stefanbaur/grannophone/case/sheet_4_siedle_noamp.pdf

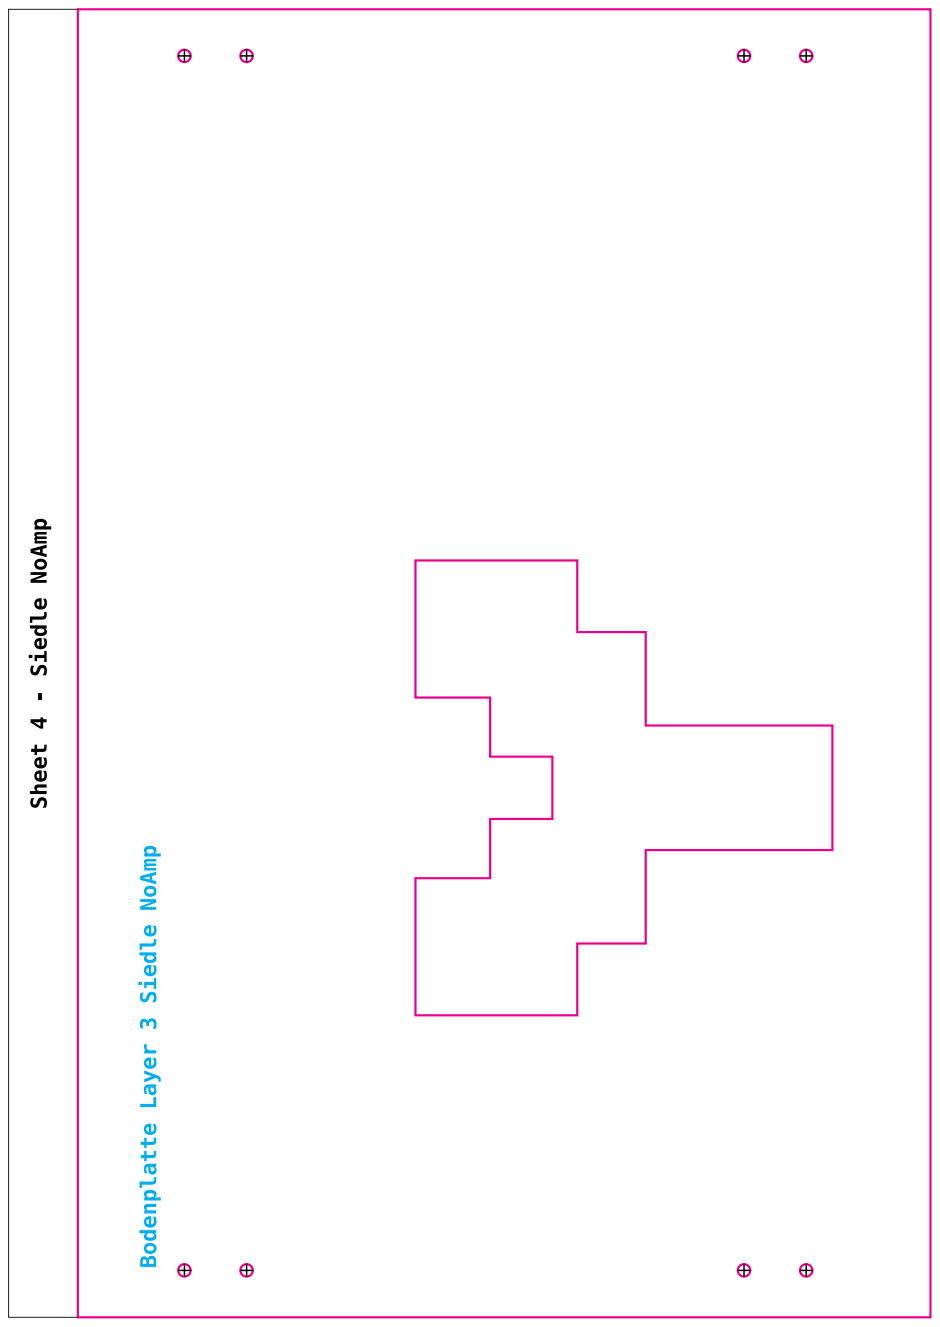
[picture p11: page 1]
