stefanbaur/grannophone/case/sheet_4_veco.pdf

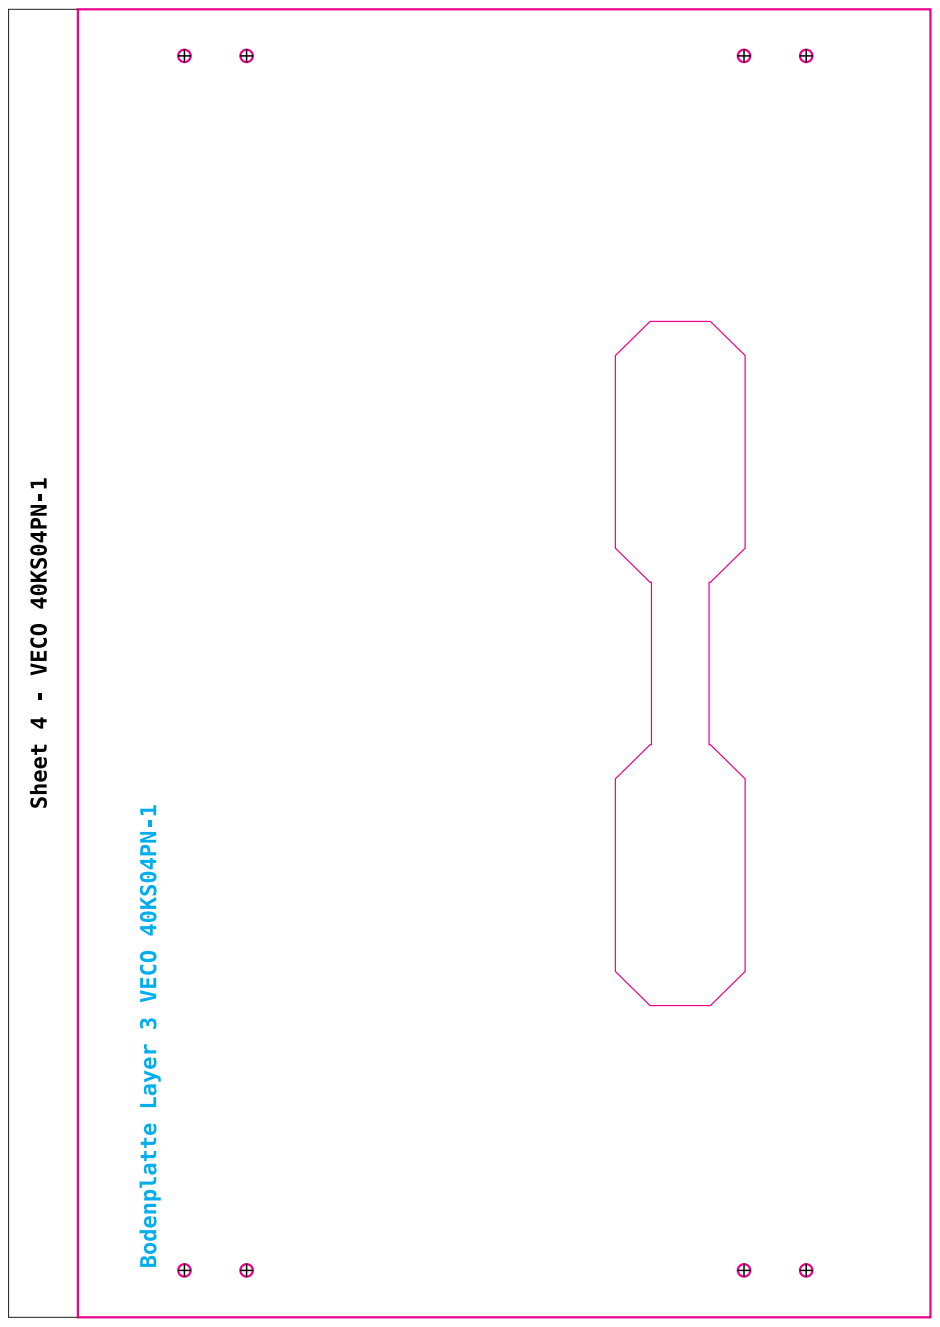
[picture p12: page 1]
