stefanbaur/grannophone/case/sheet_4_visaton_waveshare.pdf

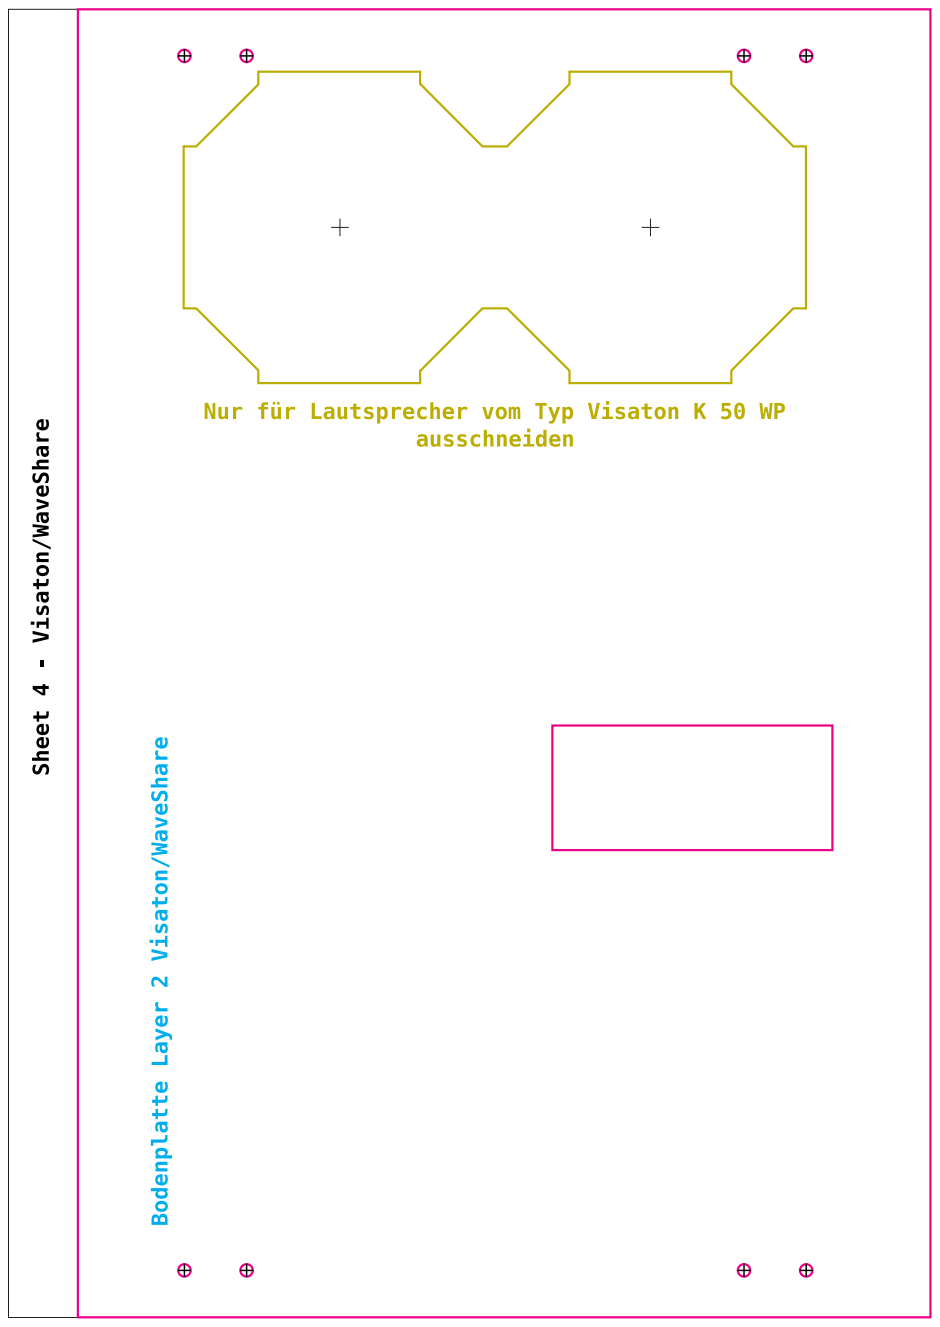
[picture p13: page 1]
