stefanbaur/grannophone/case/sheet_5_siedle_noamp.pdf

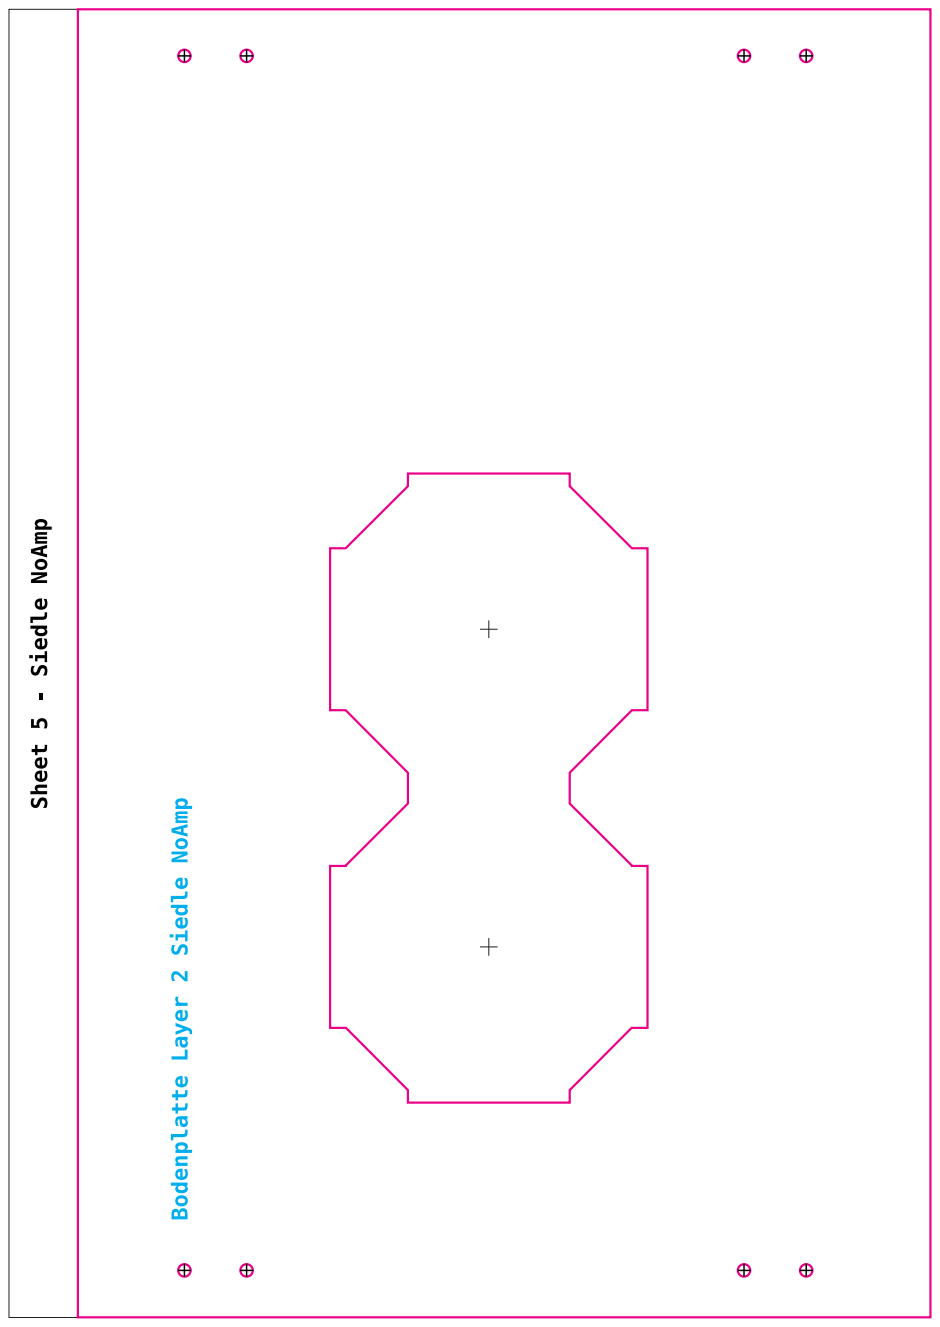
[picture p14: page 1]
