stefanbaur/grannophone/case/sheet_5_veco.pdf

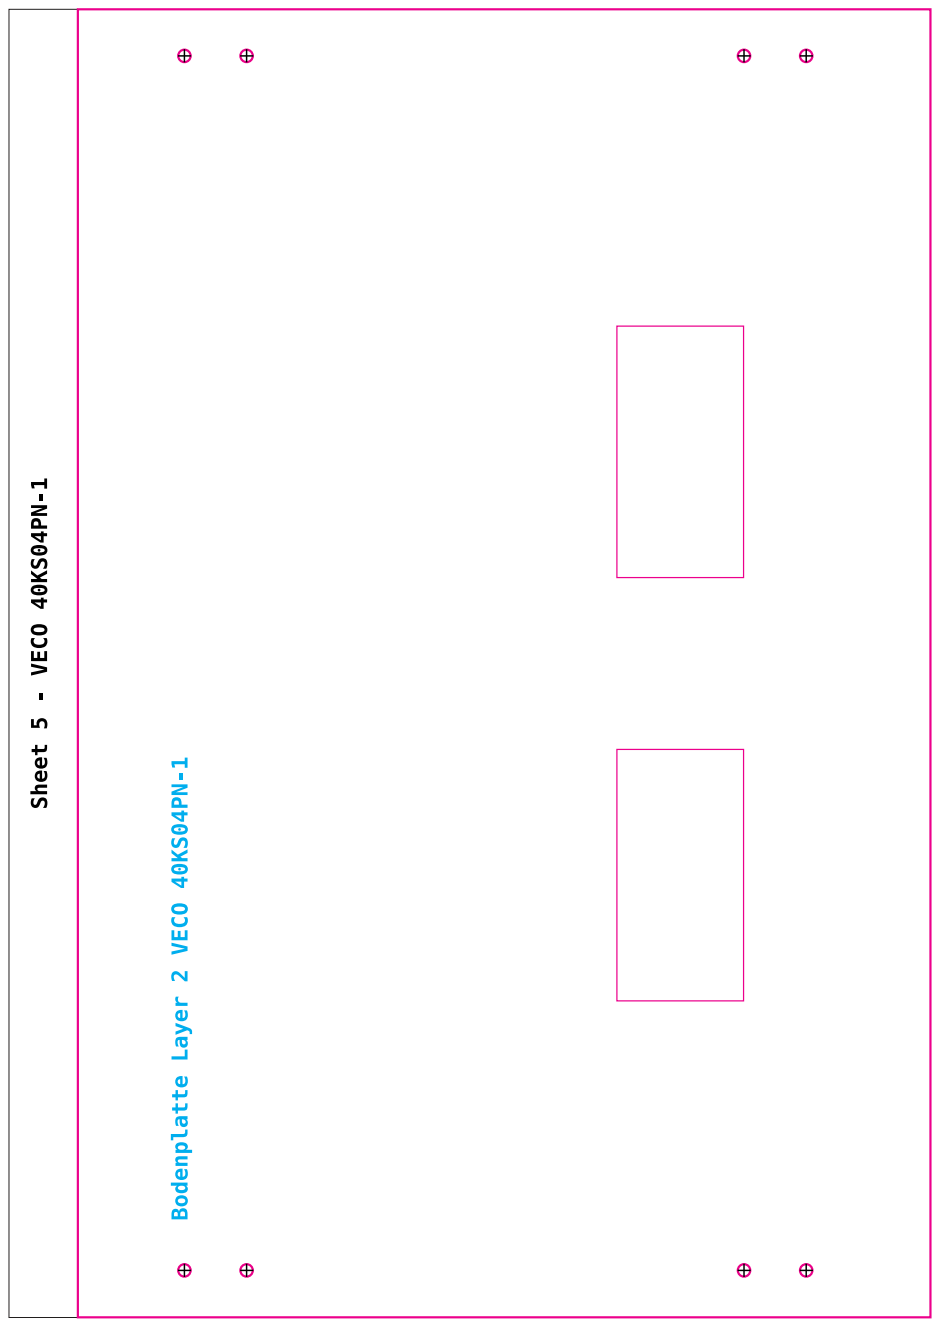
[picture p15: page 1]
