stefanbaur/grannophone/case/sheet_5_visaton.pdf

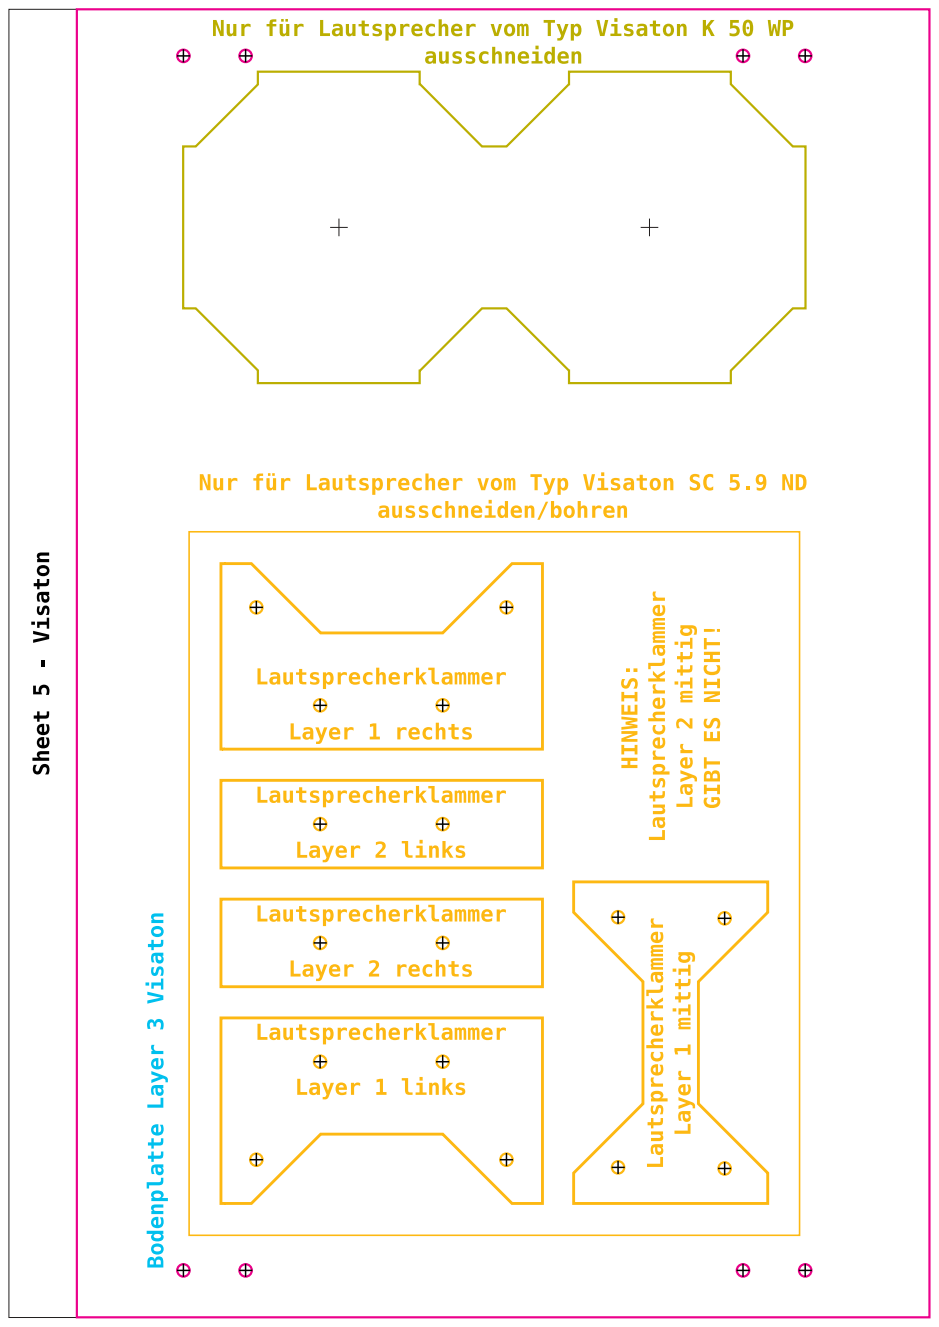
[picture p16: page 1]
