stefanbaur/grannophone/case/sheet_5_waveshare.pdf

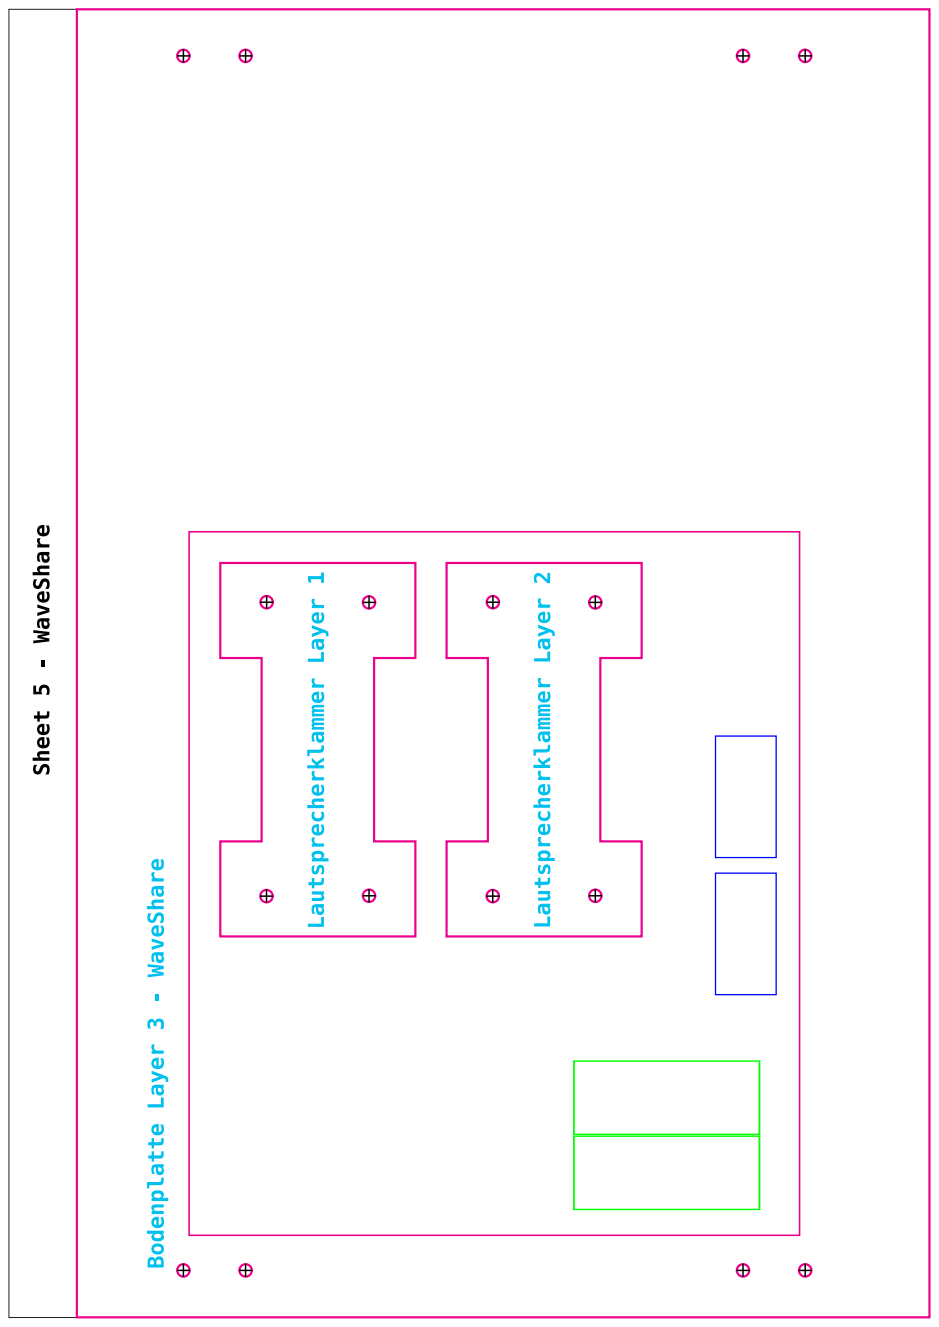
[picture p17: page 1]
