stefanbaur/grannophone/case/sheet_6_siedle_noamp.pdf

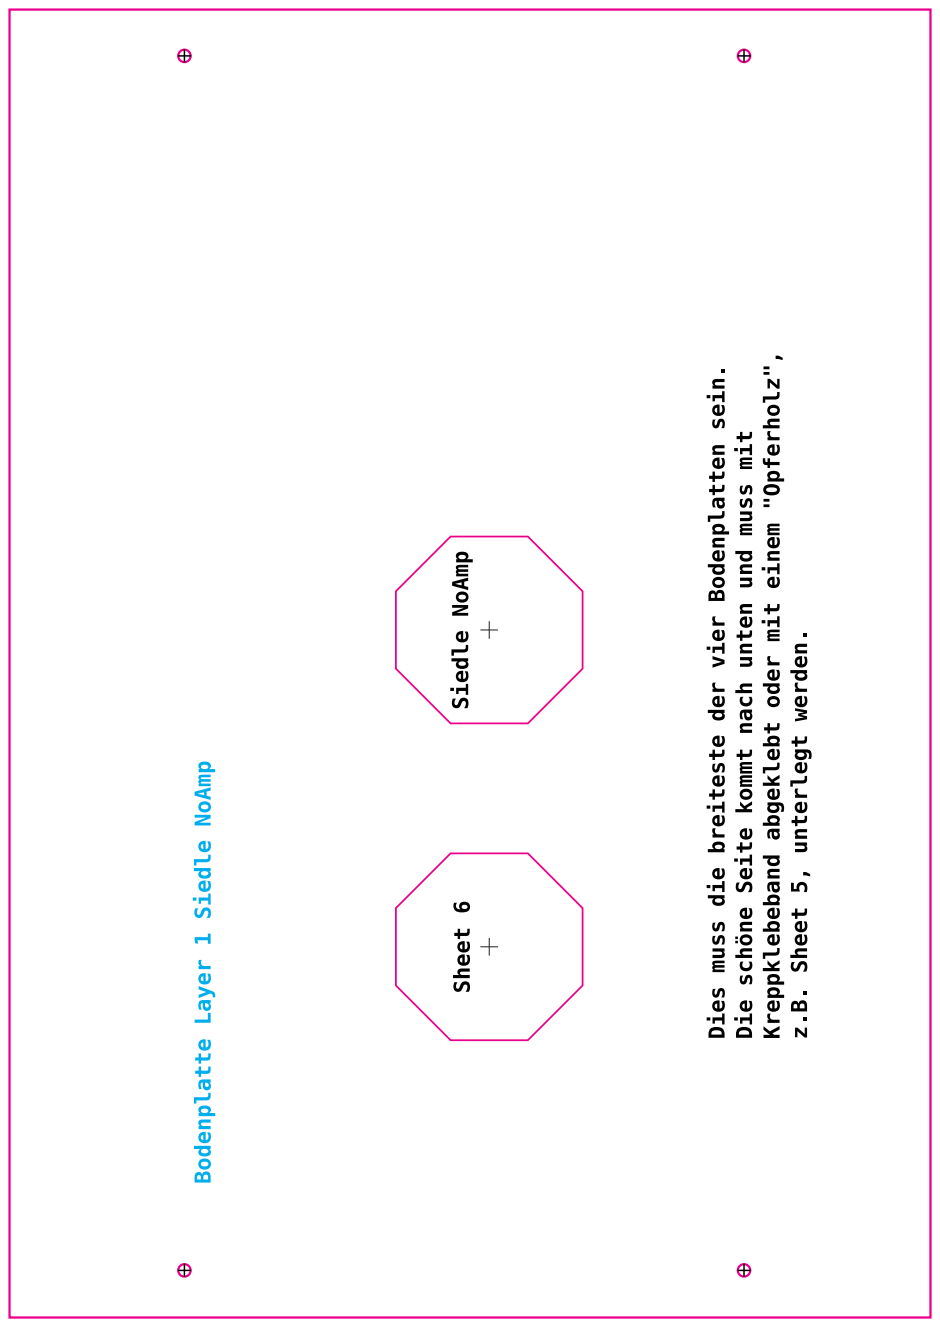
[picture p18: page 1]
