stefanbaur/grannophone/case/sheet_6_veco.pdf

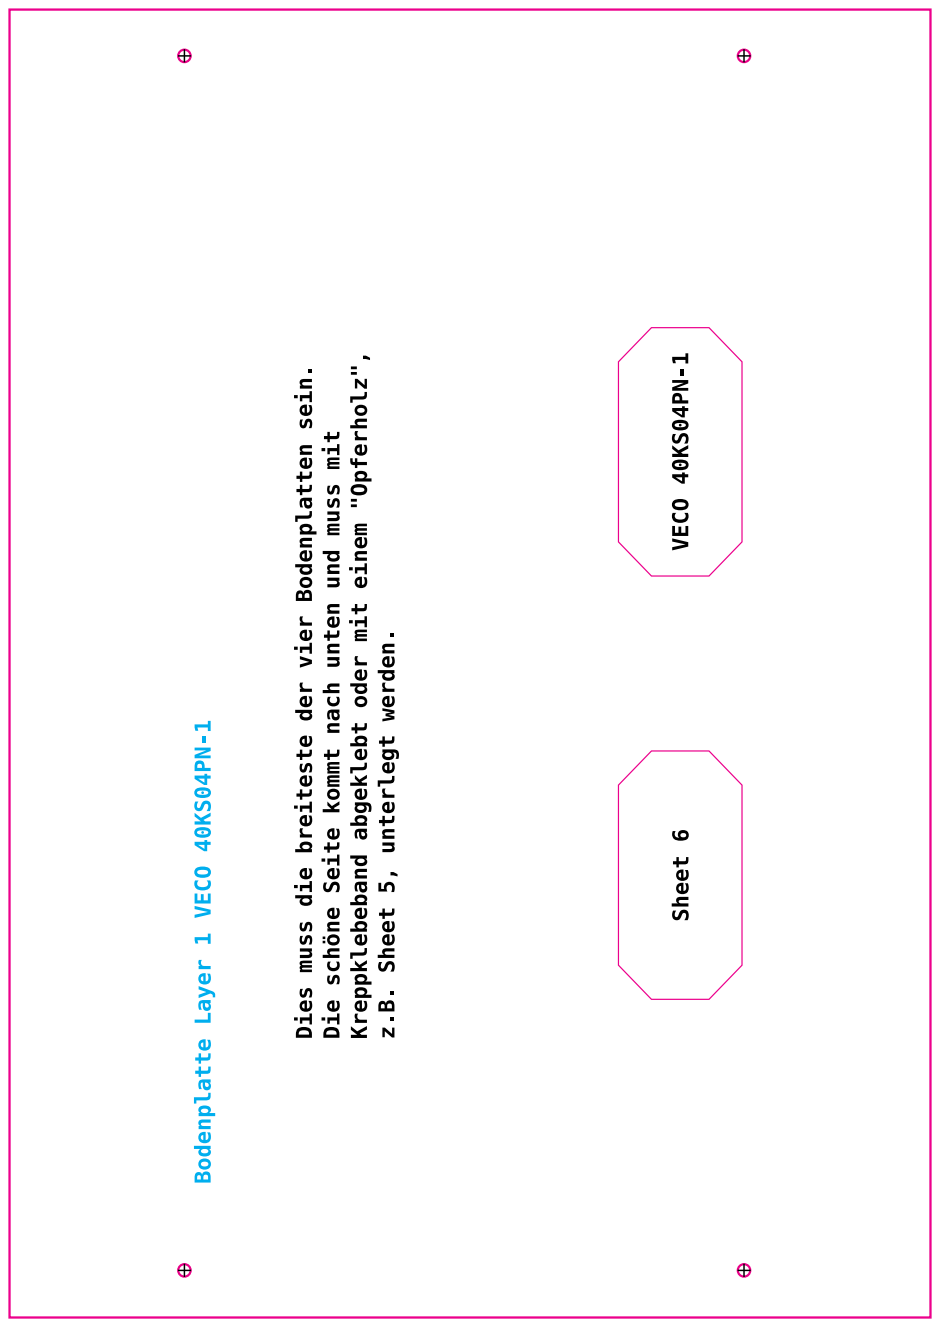
[picture p19: page 1]
