stefanbaur/grannophone/case/sheet_6_visaton_waveshare.pdf

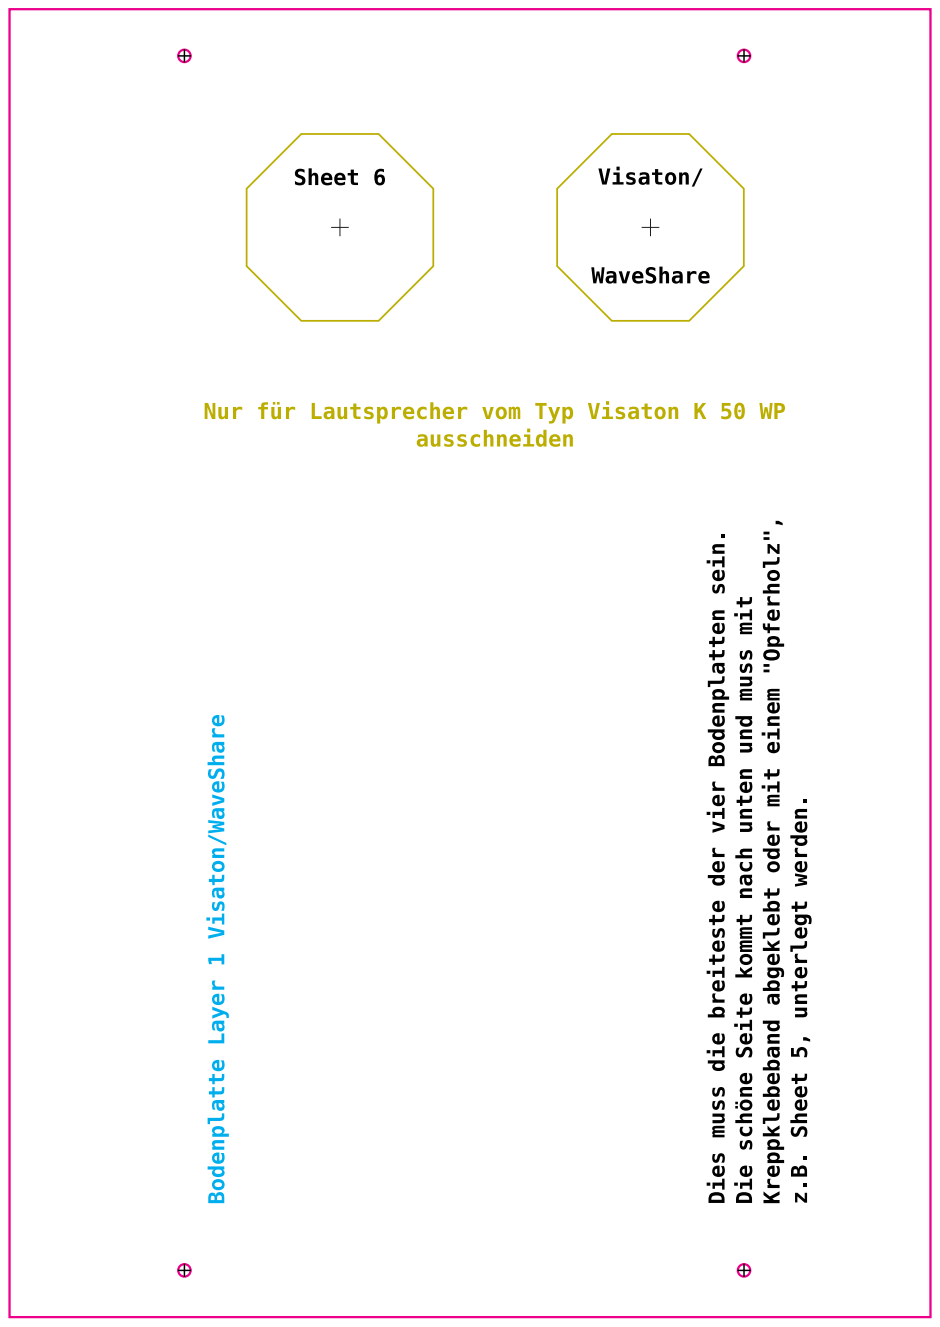
[picture p20: page 1]
