stefanbaur/grannophone/case/sheet_7.pdf

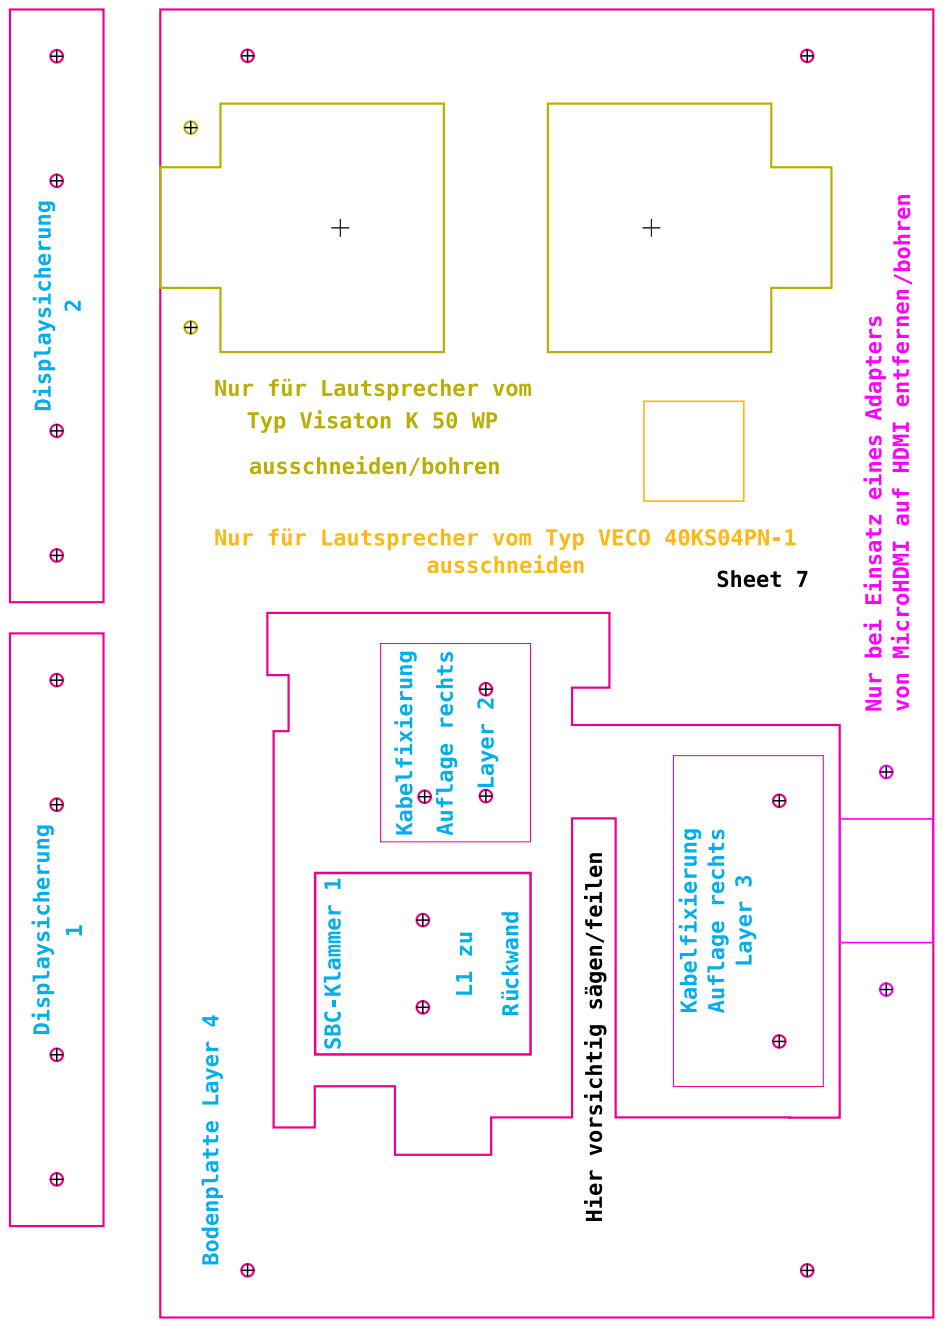
[picture p21: page 1]
