stefanbaur/grannophone/case/sheet_8.pdf

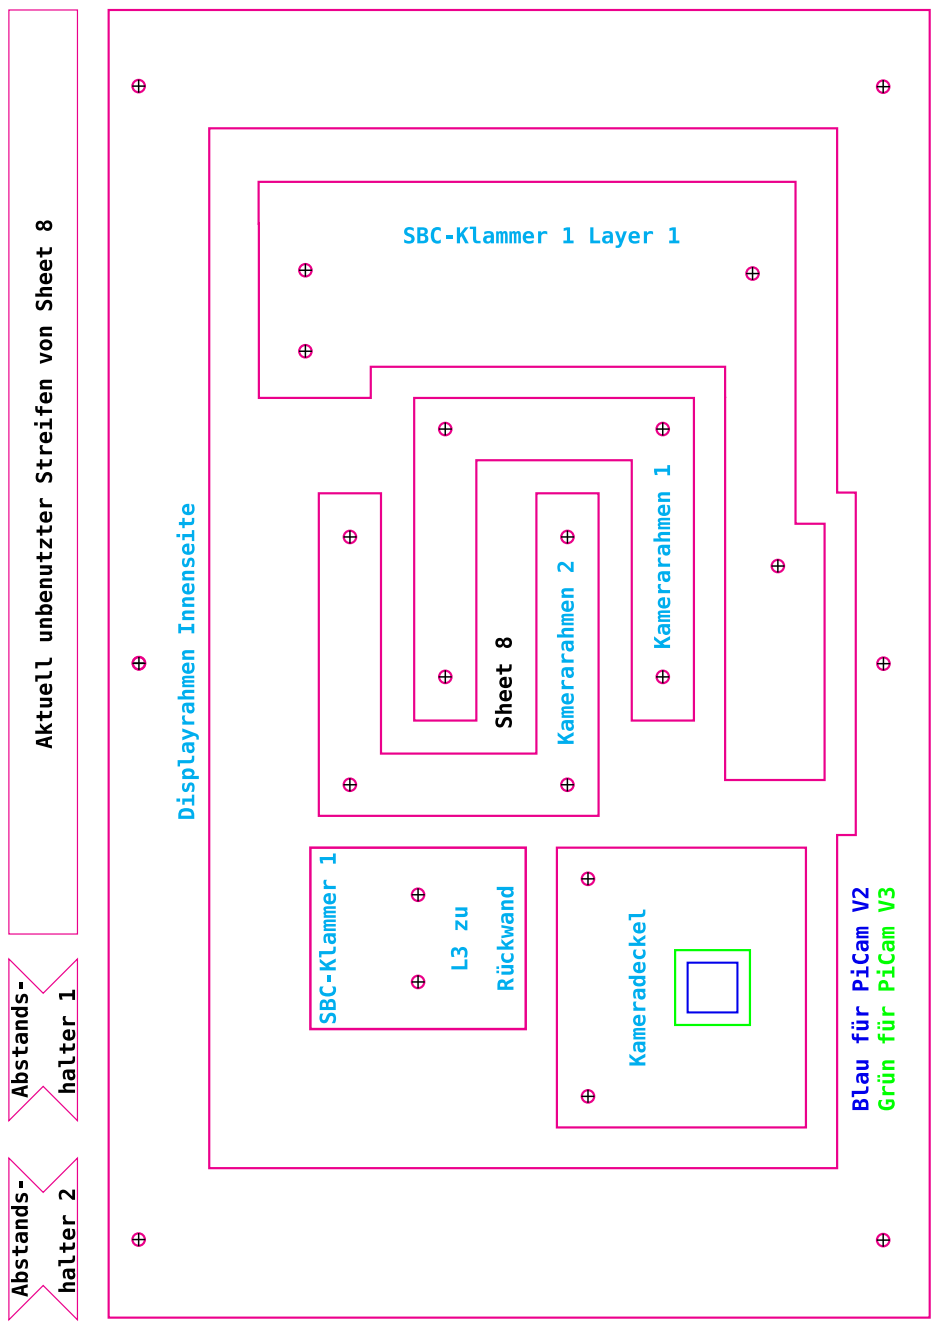
[picture p22: page 1]
