stefanbaur/grannophone/case/sheet_8_buttons.pdf

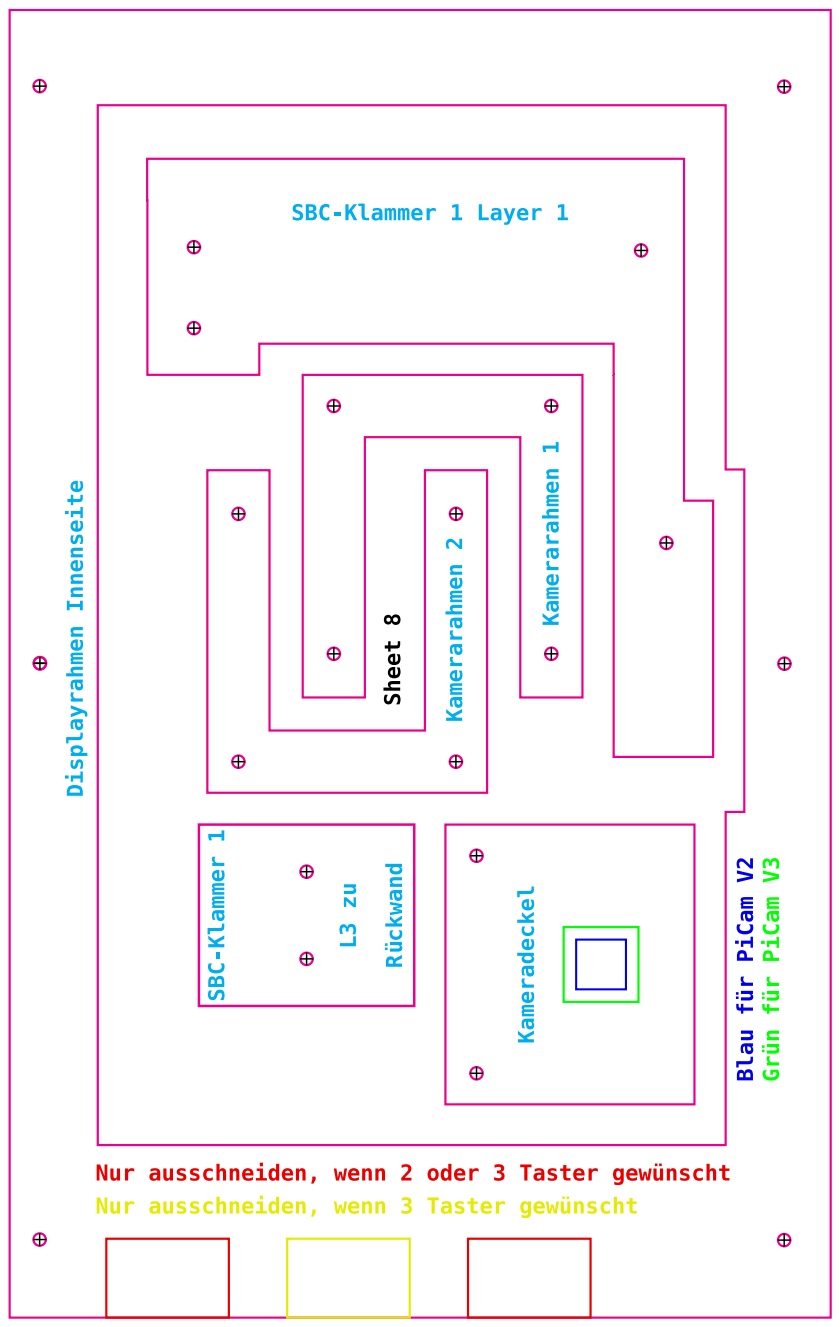
[picture p23: page 1]
