stefanbaur/grannophone/case/sheet_9_digitus.pdf

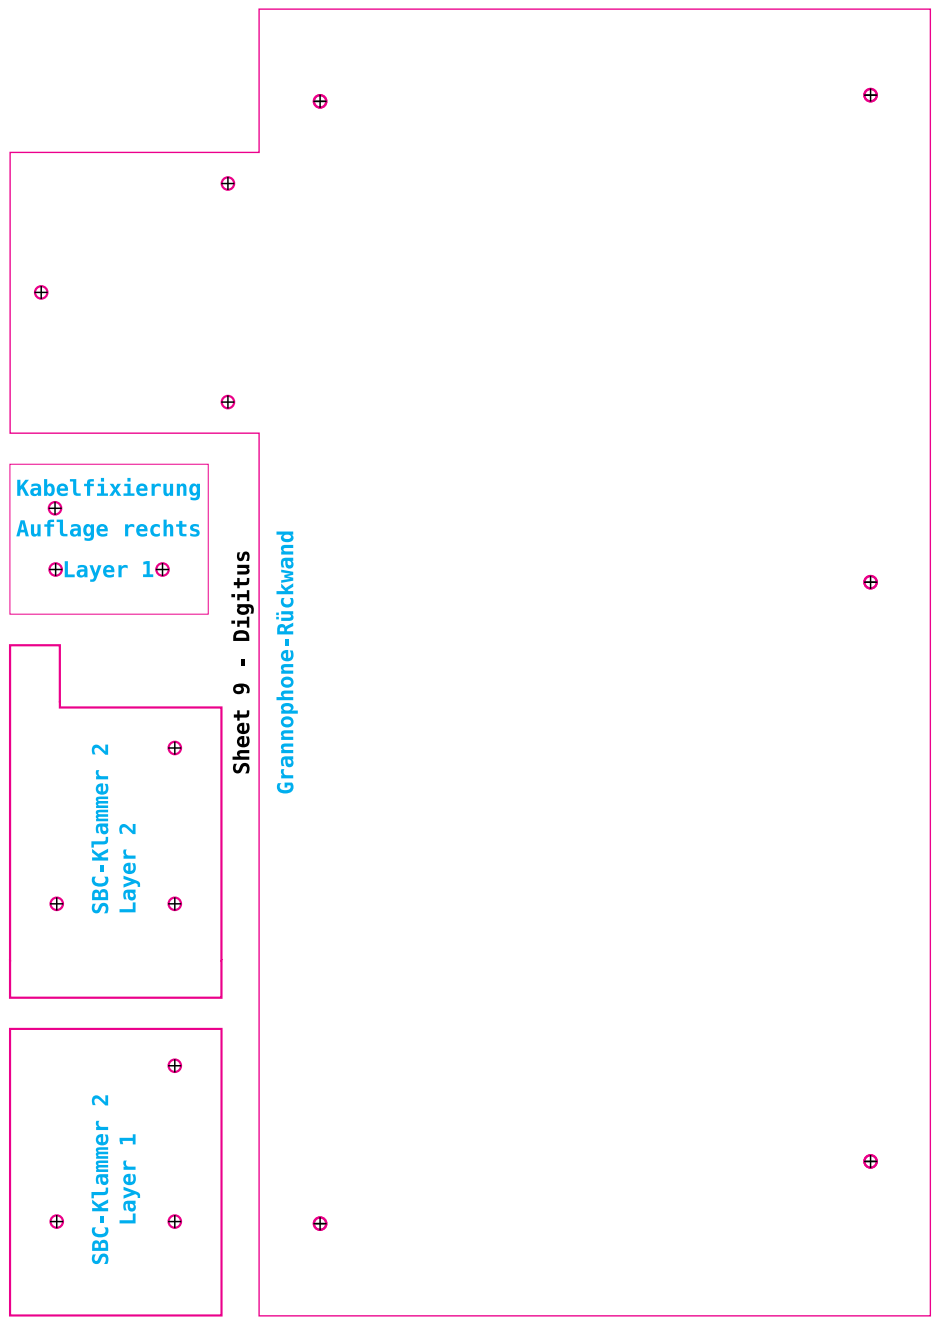
[picture p24: page 1]
