stefanbaur/grannophone/case/sheet_9_digitus_visaton.pdf

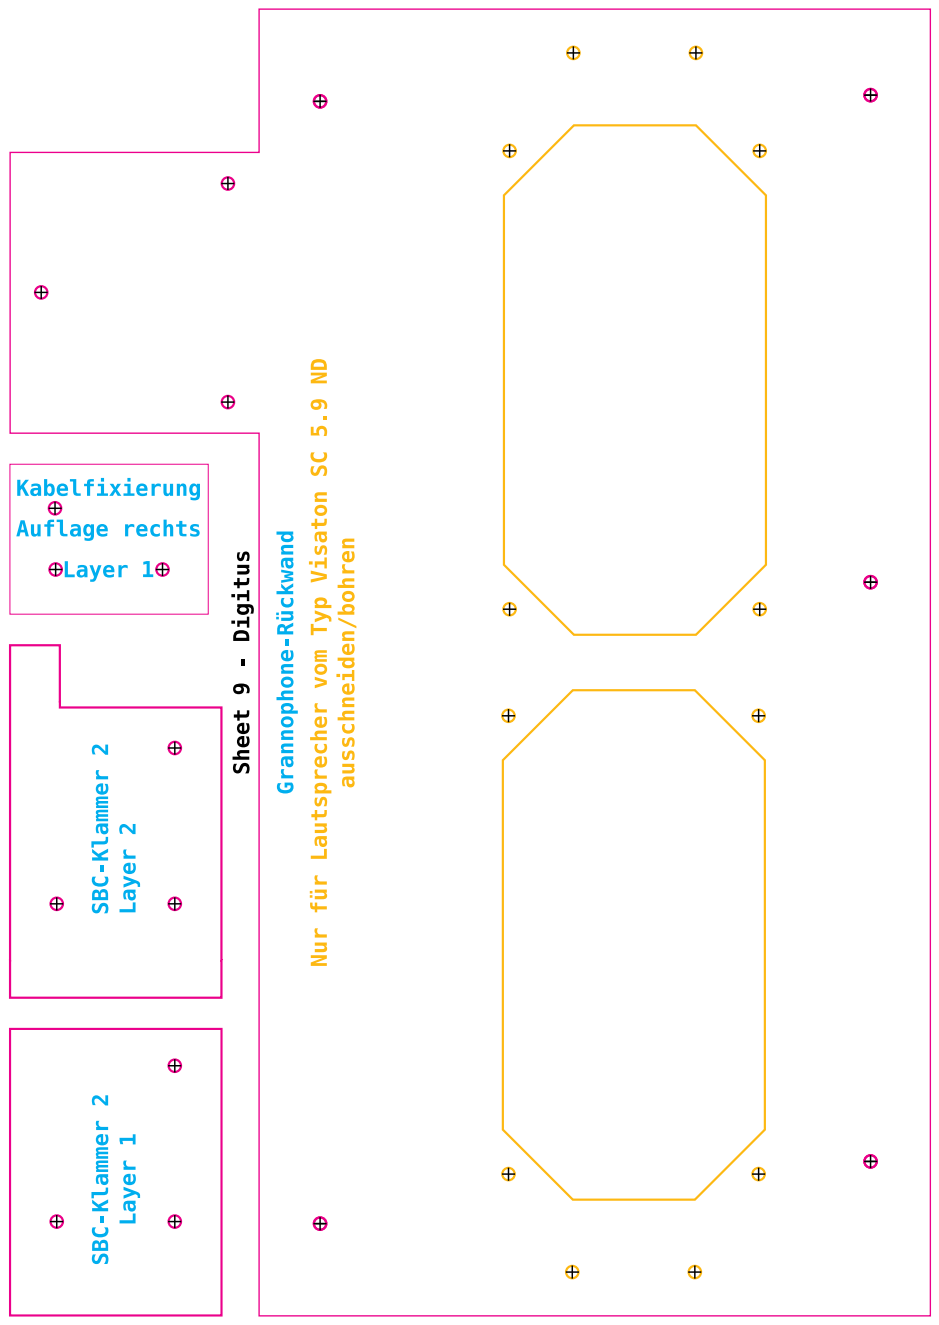
[picture p25: page 1]
