stefanbaur/grannophone/case/sheet_9_digitus_waveshare.pdf

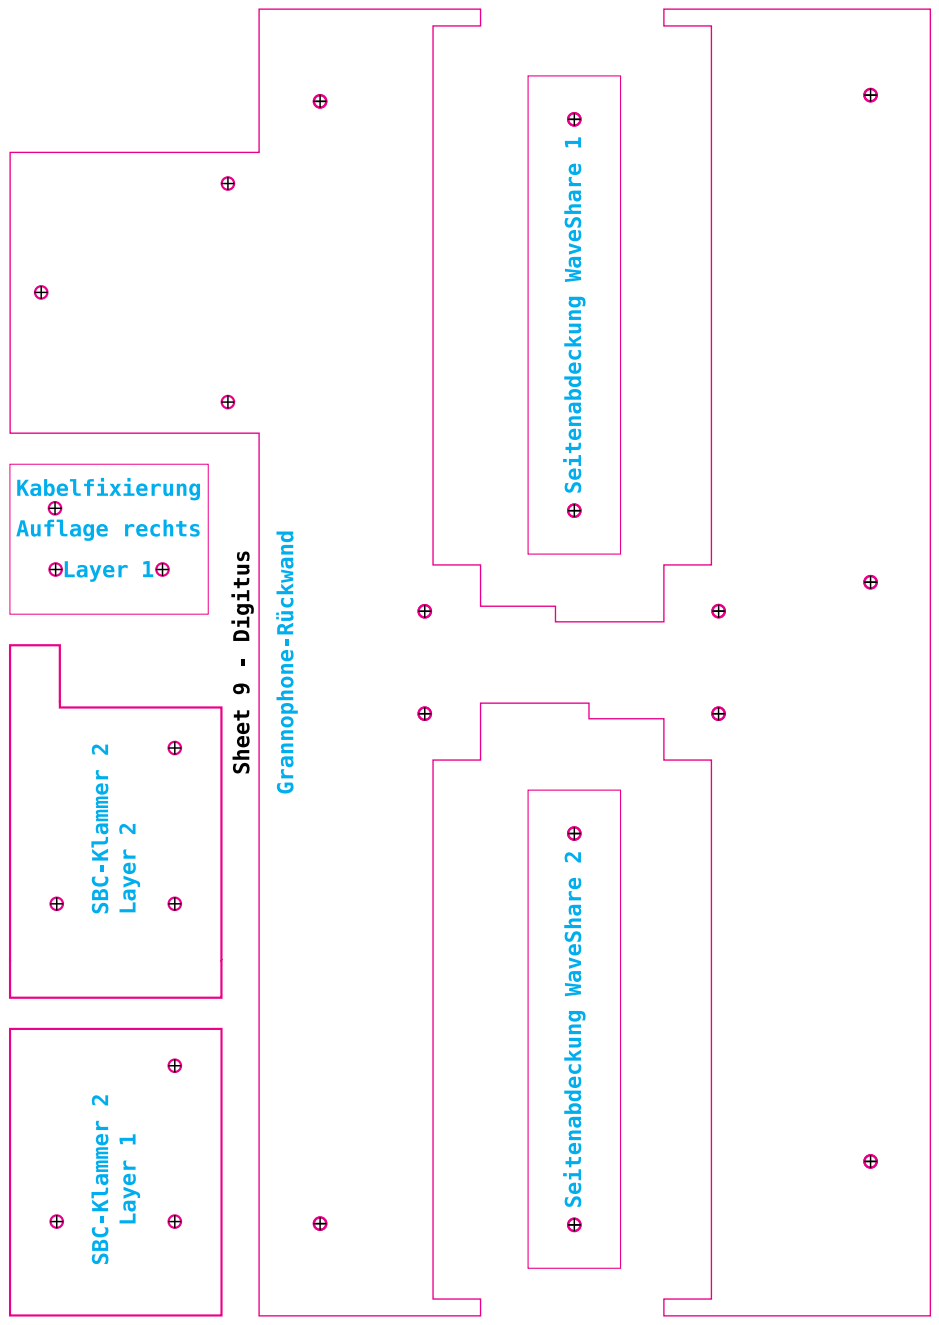
[picture p26: page 1]
