stefanbaur/grannophone/case/sheet_9_opistech.pdf

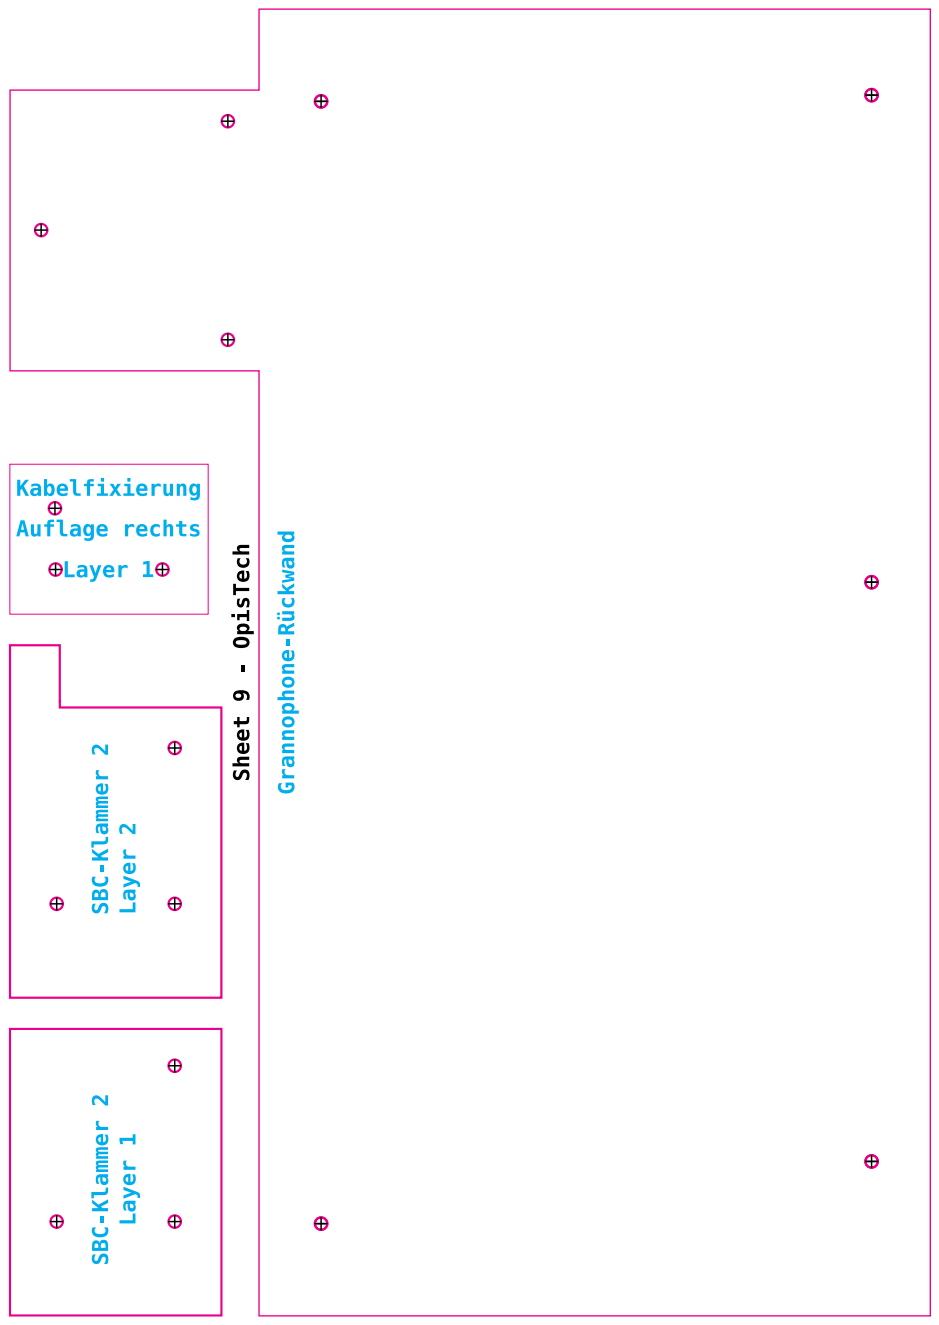
[picture p27: page 1]
