stefanbaur/grannophone/case/sheet_9_opistech_visaton.pdf

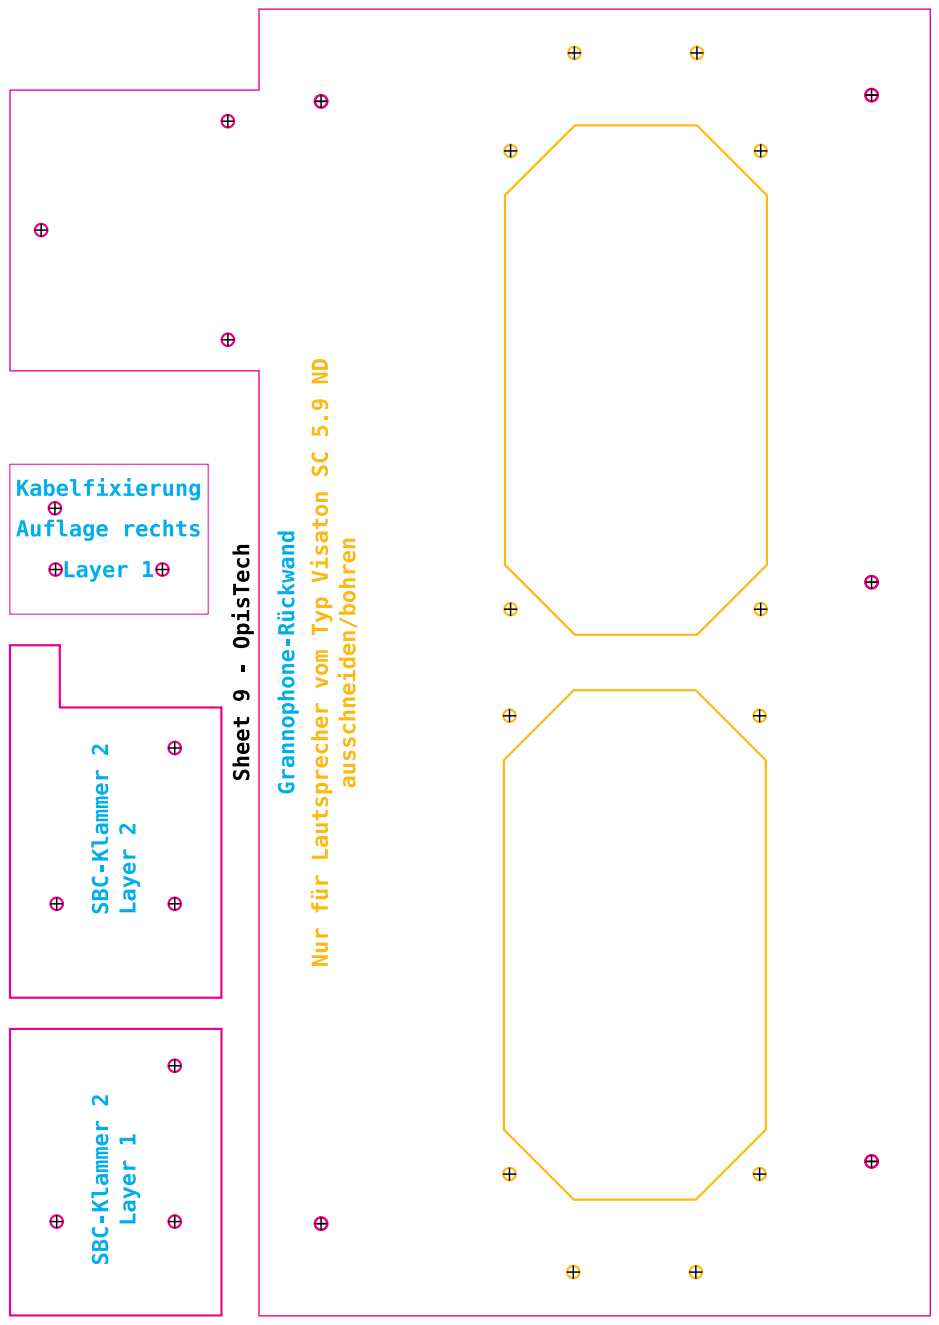
[picture p28: page 1]
