stefanbaur/grannophone/case/sheet_9_opistech_waveshare.pdf

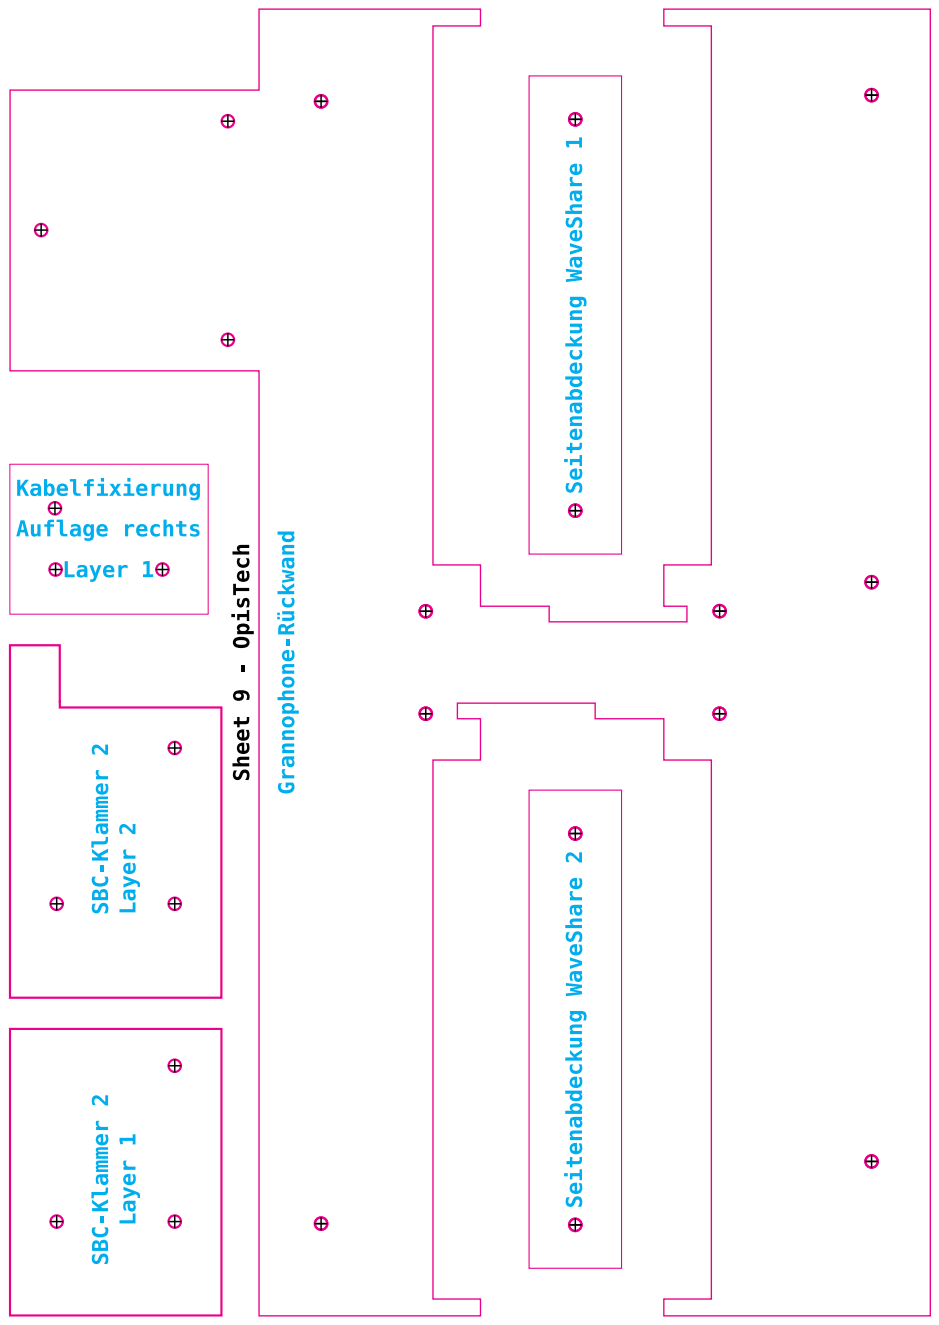
[picture p29: page 1]
