stefanbaur/grannophone/heatsink/heatsink.pdf

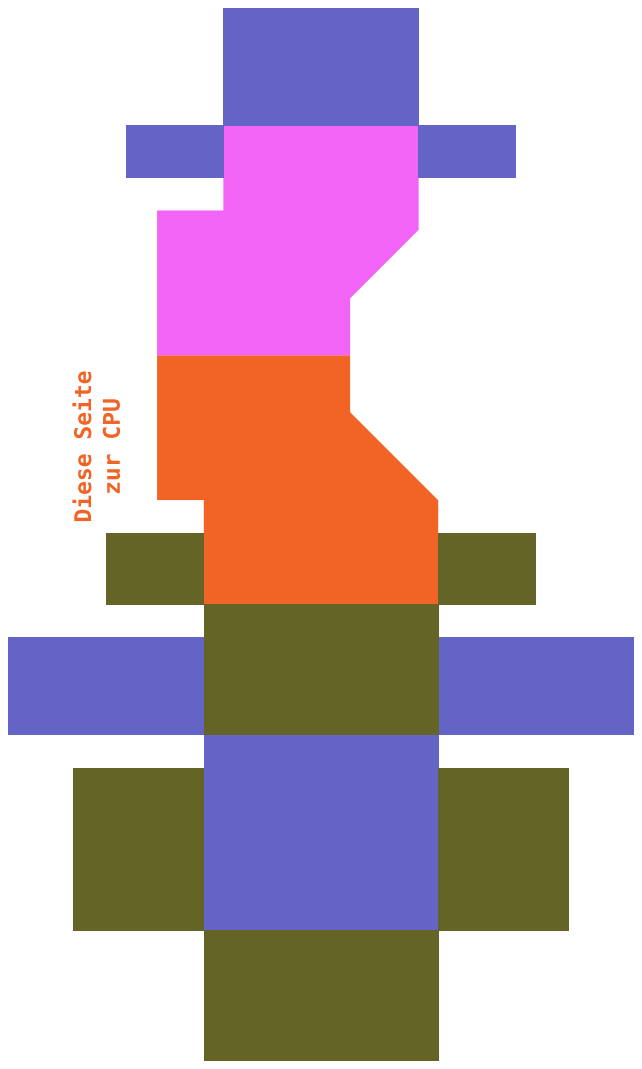
[picture p30: page 1]
