stefanbaur/grannophone/handset/sheet_a_ekulit_visaton_siedle_delock_logilink_usb.pdf

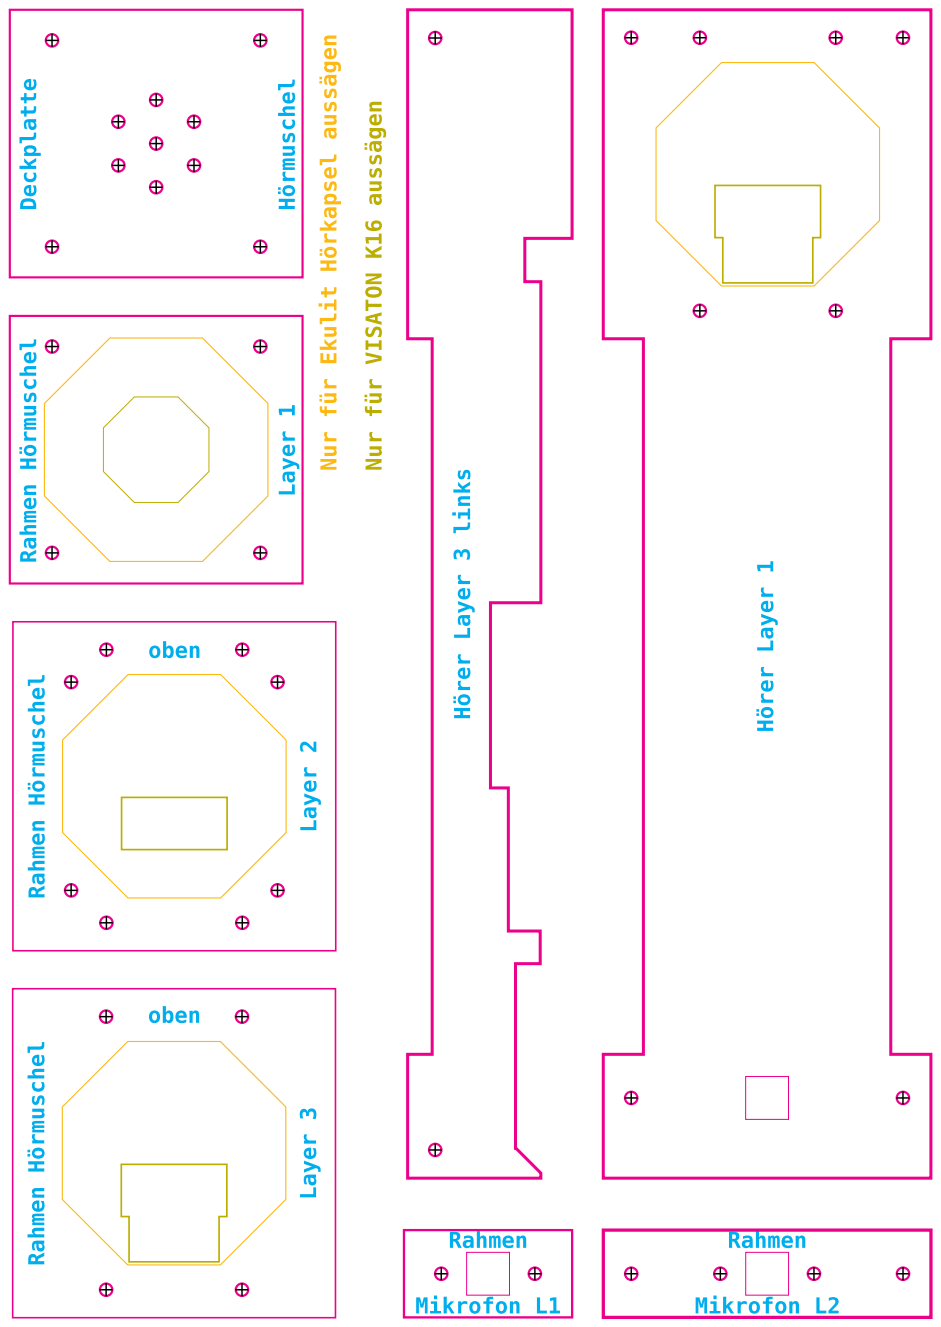
[picture p31: page 1]
