stefanbaur/grannophone/handset/sheet_a_ekulit_visaton_siedle_wago_trrs.pdf

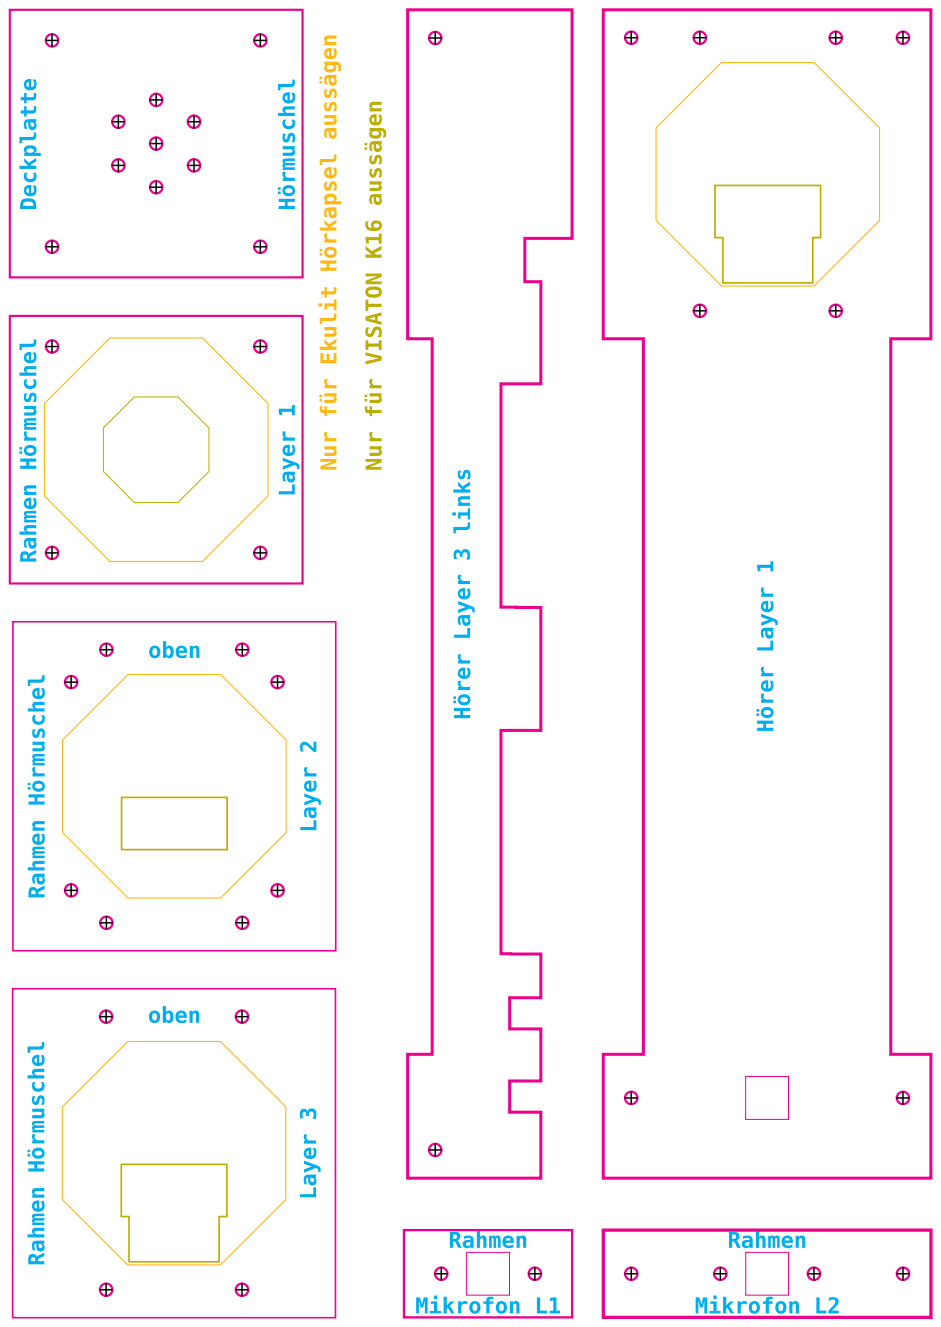
[picture p32: page 1]
