stefanbaur/grannophone/handset/sheet_b_ekulit_visaton_siedle_delock_logilink_usb.pdf

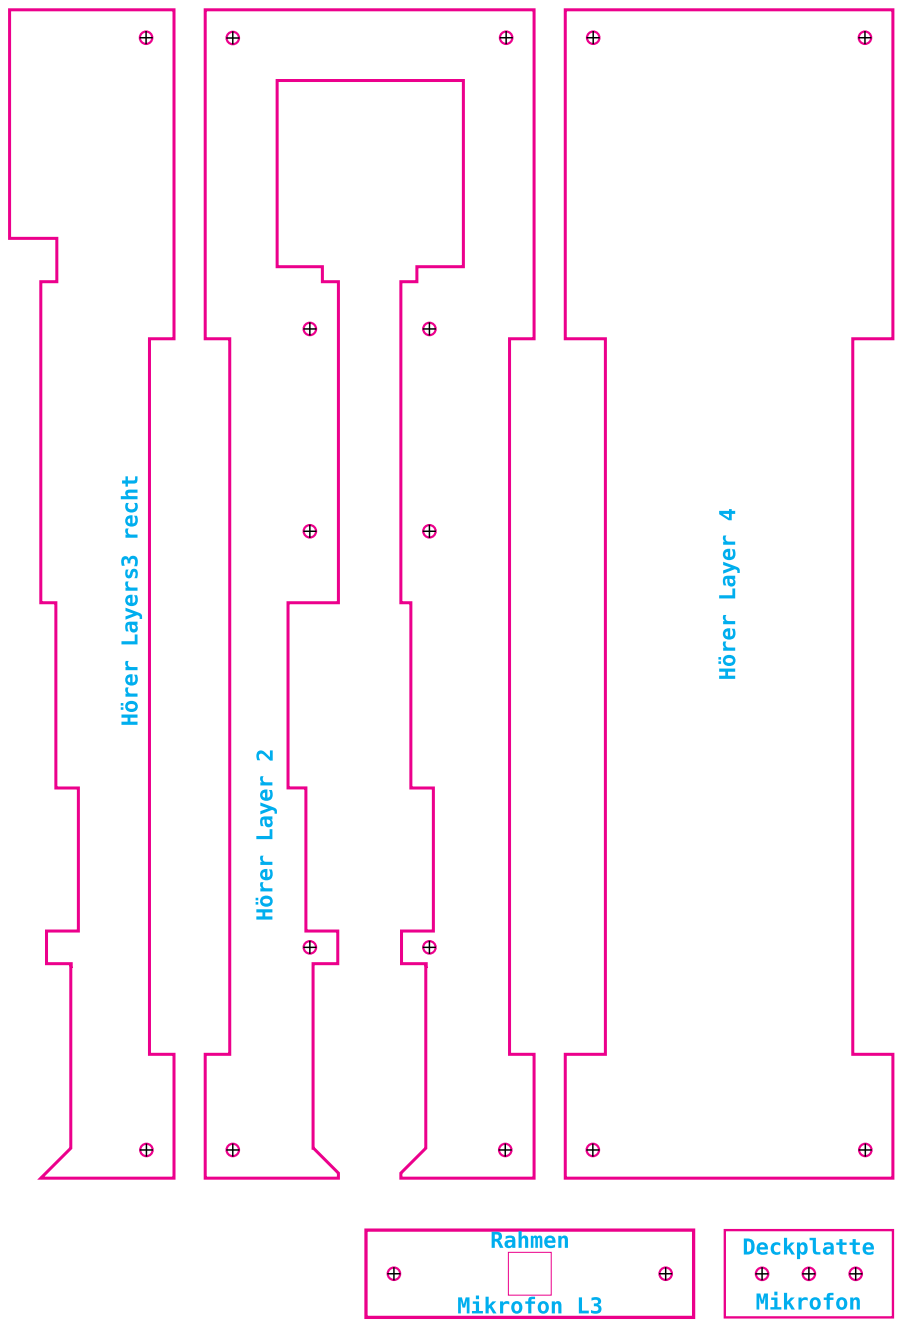
[picture p33: page 1]
