stefanbaur/grannophone/handset/sheet_b_ekulit_visaton_siedle_wago_trrs.pdf

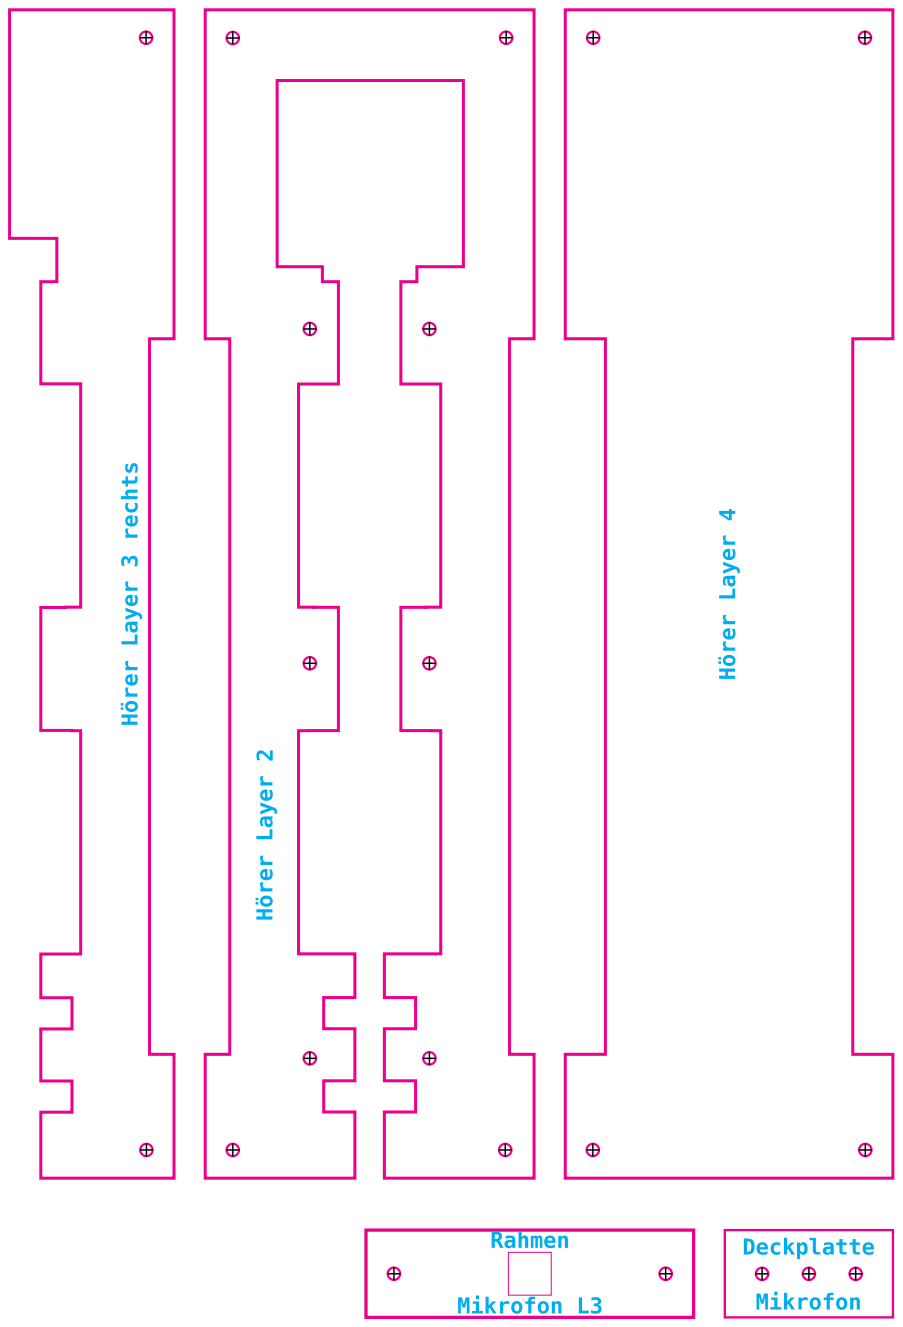
[picture p34: page 1]
